CrashOverrideProductions/Bad_USB_W/images/IMG_20210702_203633.jpg

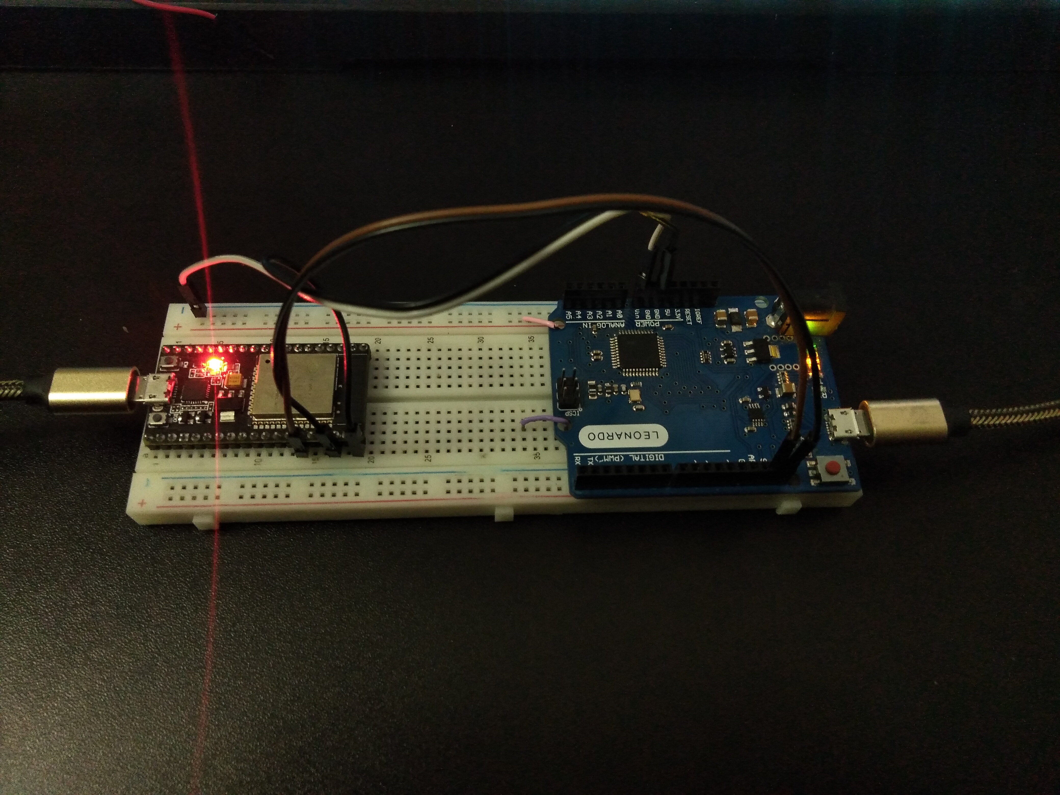
images/IMG_20210702_203633.jpg
