CrashOverrideProductions/Bad_USB_W/Software/PlatformIO/esp_duck/src/spiffs.cpp

/*
   This software is licensed under the MIT License. See the license file for details.
   Source: https://github.com/spacehuhntech/WiFiDuck
 */

#include "spiffs.h"

#include "config.h"
#include "debug.h"

namespace spiffs {
    File streamFile;

    // ===== PRIVATE ===== //
    void fixPath(String& path) {
        if (!path.startsWith("/")) {
            path = "/" + path;
        }
    }

    // ===== PUBLIC ====== //
    void begin() {
        debug("Initializing SPIFFS...");
        SPIFFS.begin();
        debugln("OK");

        String FILE_NAME = "/startup_spiffs_test.txt";

        remove(FILE_NAME);
        create(FILE_NAME);
        File f = open(FILE_NAME);
        if (!f) {
            format();
        } else {
            f.close();
            remove(FILE_NAME);
        }
    }

    void format() {
        debug("Formatting SPIFFS...");
        SPIFFS.format();
        debugln("OK");
    }

    size_t size() {
        unsigned int totalBytes = SPIFFS.totalBytes();
        return totalBytes;
    }

    size_t usedBytes() {
        unsigned int usedBytes = SPIFFS.usedBytes();
        return usedBytes;
    }

    size_t freeBytes() {
        unsigned int totalBytes = SPIFFS.totalBytes();
        unsigned int usedBytes = SPIFFS.usedBytes();

        return (totalBytes - usedBytes);
    }

    size_t size(String fileName) {
        fixPath(fileName);

        File f = SPIFFS.open(fileName, FILE_READ);

        return f.size();
    }

    bool exists(String fileName) {
        return SPIFFS.exists(fileName);
    }

    File open(String fileName) {
        fixPath(fileName);

        File file = SPIFFS.open(fileName, "r+");
        // debug("File Contents: ");
        // debugln(file.name());
        // debug(file);

        return file;
    }

    void create(String fileName) {
        fixPath(fileName);

        File f = SPIFFS.open(fileName, FILE_APPEND);

        f.close();
    }

    void remove(String fileName) {
        fixPath(fileName);

        SPIFFS.remove(fileName);
        
    }

    void rename(String oldName, String newName) {
        fixPath(oldName);
        fixPath(newName);

        SPIFFS.rename(oldName, newName);
    }

    void write(String fileName, const char* str) {
        File f = open(fileName);

        if (f) {
            f.println(str);
            f.close();
            debugln("Wrote file");
        } else {
            debugln("File error");
        }
    }

    void write(String fileName, const uint8_t* buf, size_t len) {
        File f = open(fileName);

        if (f) {
            f.write(buf, len);
            f.close();
            debugln("Wrote file");
        } else {
            debugln("File error");
        }
    }

   


String listDir(String dirName) {
    String res;

    fixPath(dirName);

    File root = SPIFFS.open(dirName);
   
    if(!root)
    {
      debugln("failed to open directory");
      return("Error!");
   }

    File file = root.openNextFile();
    while(file)
    {
        //debugln(file.name());
        res += file.name();
        res += ' ';
        res += size(file.name());
        res += '\n';
               
        file = root.openNextFile();
    }

    if (res.length() == 0) 
    {
        res += "\n";
    }
        return res;
}

    void streamOpen(String fileName) {
        streamClose();
        streamFile = open(fileName);
        if (!streamFile) debugln("ERROR: No stream file open");
    }

    void streamWrite(const char* buf, size_t len) {
        if (streamFile) streamFile.write((uint8_t*)buf, len);
        else debugln("ERROR: No stream file open");
    }

    size_t streamRead(char* buf, size_t len) {
        if (streamFile) {
            size_t i;

            for (i = 0; i<len; ++i) {
                if (!streamFile.available() || (i == len-1)) {
                    buf[i] = '\0';
                    break;
                } else {
                    buf[i] = streamFile.read();
                }
            }

            return i;
        } else {
            debugln("ERROR: No stream file open");
            return 0;
        }
    }

    size_t streamReadUntil(char* buf, char delimiter, size_t max_len) {
        if (streamFile) {
            size_t i;
            char   c = 'x';

            for (i = 0; i<max_len; ++i) {
                if ((c == delimiter) || !streamFile.available() || (i == max_len-1)) {
                    buf[i] = '\0';
                    break;
                } else {
                    c      = streamFile.read();
                    buf[i] = c;
                }
            }

            return i;
        } else {
            debugln("ERROR: No stream file open");
            return 0;
        }
    }

    void streamClose() {
        streamFile.close();
    }

    bool streaming() {
        return streamFile;
    }

    size_t streamAvailable() {
        if (!streamFile) return 0;
        return streamFile.available();
    }
}
