CrashOverrideProductions/Bad_USB_W/Software/PlatformIO/esp_duck/src/spiffs.h

/*
   This software is licensed under the MIT License. See the license file for details.
   Source: https://github.com/spacehuhntech/WiFiDuck
 */

#pragma once

#include <Arduino.h> // String

#include "Libraries/SPIFFS.h"
#include "Libraries/FS.h"

namespace spiffs {
    void begin();
    void format();

    size_t size();
    size_t usedBytes();
    size_t freeBytes();

    size_t size(String fileName);
    bool exists(String fileName);

    File open(String fileName);
    void create(String fileName);

    void remove(String fileName);
    void rename(String oldName, String newName);
    void write(String fileName, const char* str);
    void write(String fileName, const uint8_t* buf, size_t len);

    String listDir(String dirName);

    void streamOpen(String fileName);
    void streamWrite(const char* buf, size_t len);
    size_t streamRead(char* buf, size_t len);
    size_t streamReadUntil(char* buf, char delimiter, size_t max_len);
    void streamClose();
    bool streaming();
    size_t streamAvailable();
}
